pippomaraf/SistemiEmbedded-Carrell-Ino/images/IMG_20220301_101540.jpg

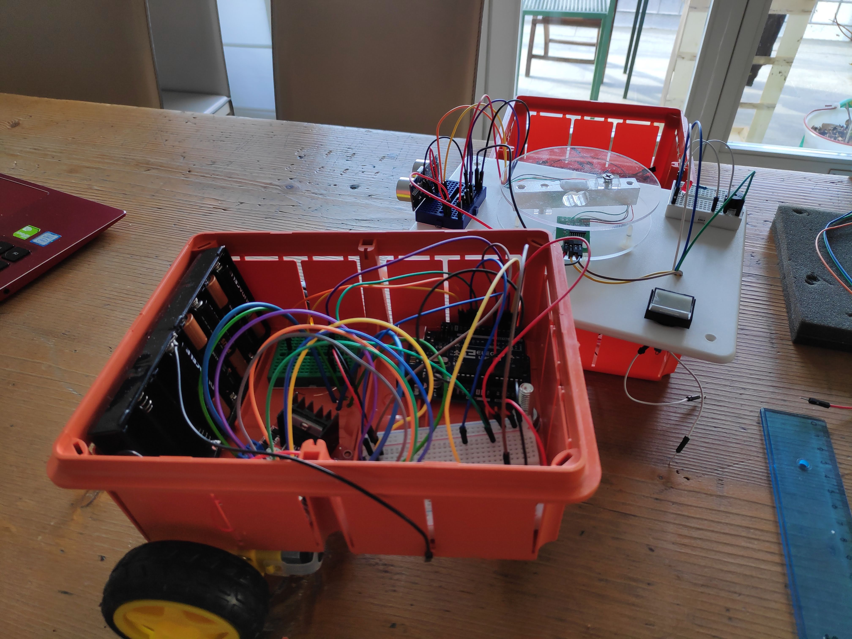
images/IMG_20220301_101540.jpg
