pippomaraf/SistemiEmbedded-Carrell-Ino/images/IMG_20220302_191206_1.jpg

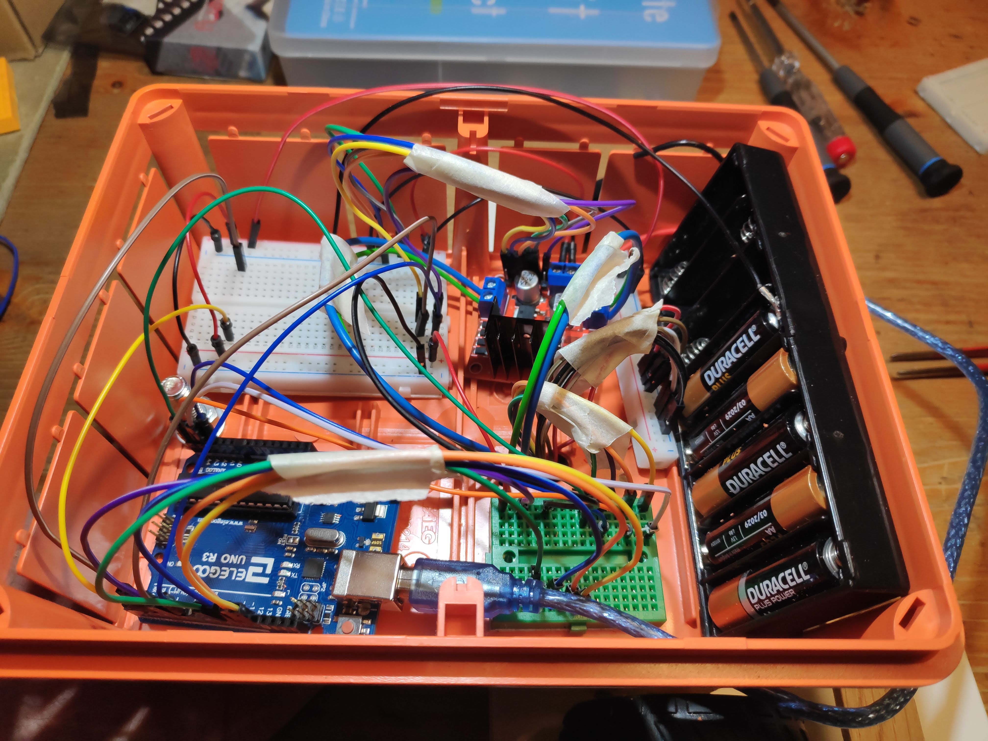
images/IMG_20220302_191206_1.jpg
