pippomaraf/SistemiEmbedded-Carrell-Ino/images/IMG_20220302_191943.jpg

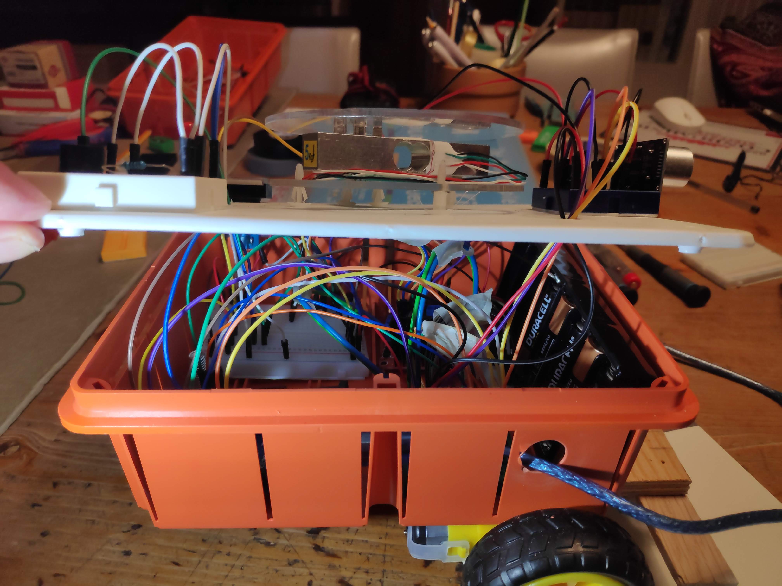
images/IMG_20220302_191943.jpg
