pippomaraf/SistemiEmbedded-Carrell-Ino/images/IMG_20221110_135122.jpg

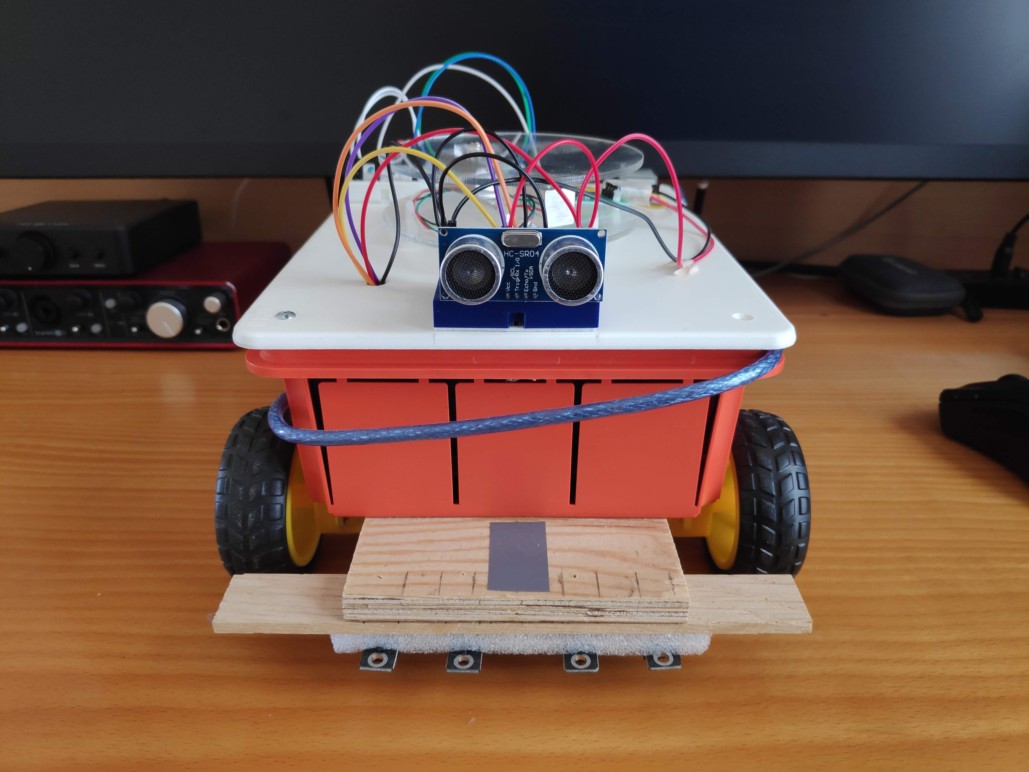
images/IMG_20221110_135122.jpg
